soupie-62/SWR_Meter/Notes/circuit-03-KiCad.png

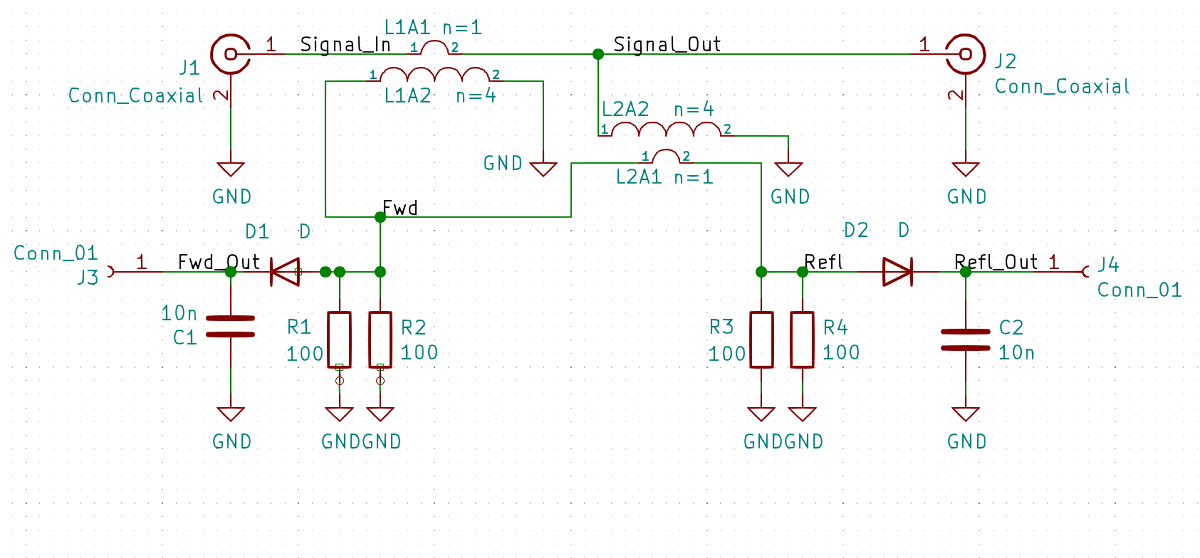
Notes/circuit-03-KiCad.png
