soupie-62/SWR_Meter/Notes/IMG_20211_1_Tin.jpg

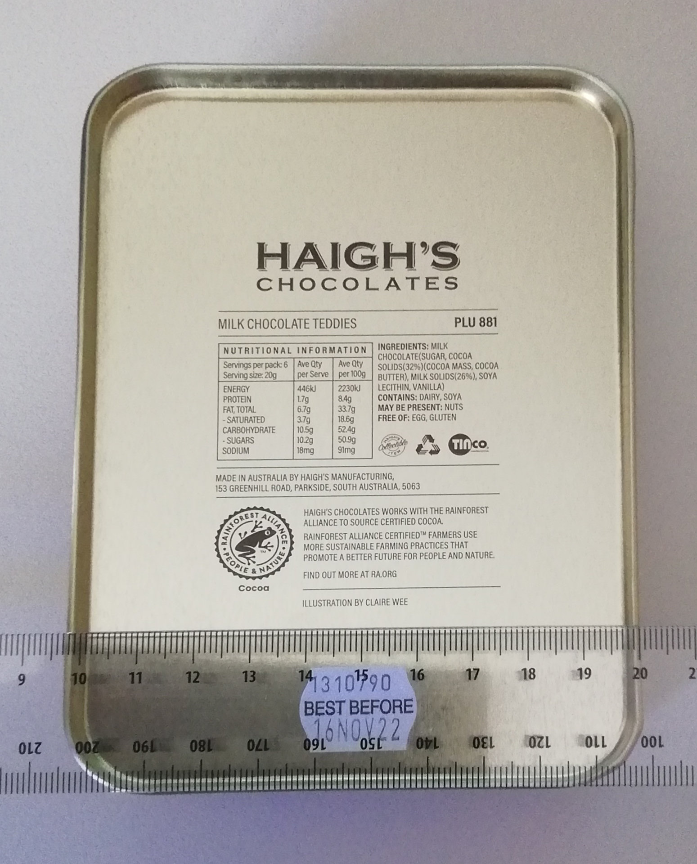
Notes/IMG_20211_1_Tin.jpg
