soupie-62/SWR_Meter/Notes/PCB_Spiral_20GHz_1.png

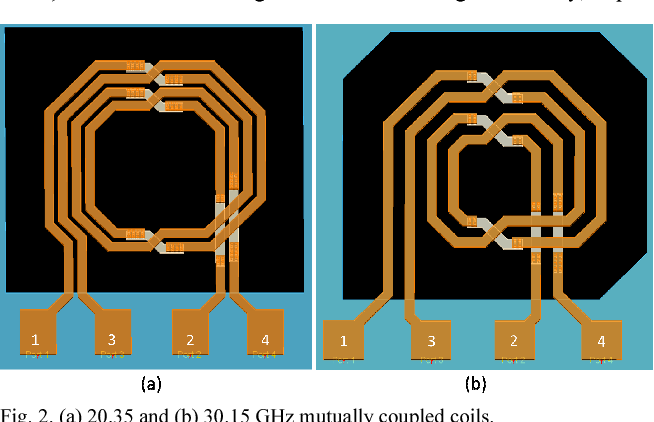
Notes/PCB_Spiral_20GHz_1.png
