soupie-62/SWR_Meter/Notes/S-Parameters - Enrico Lia 1.jpg

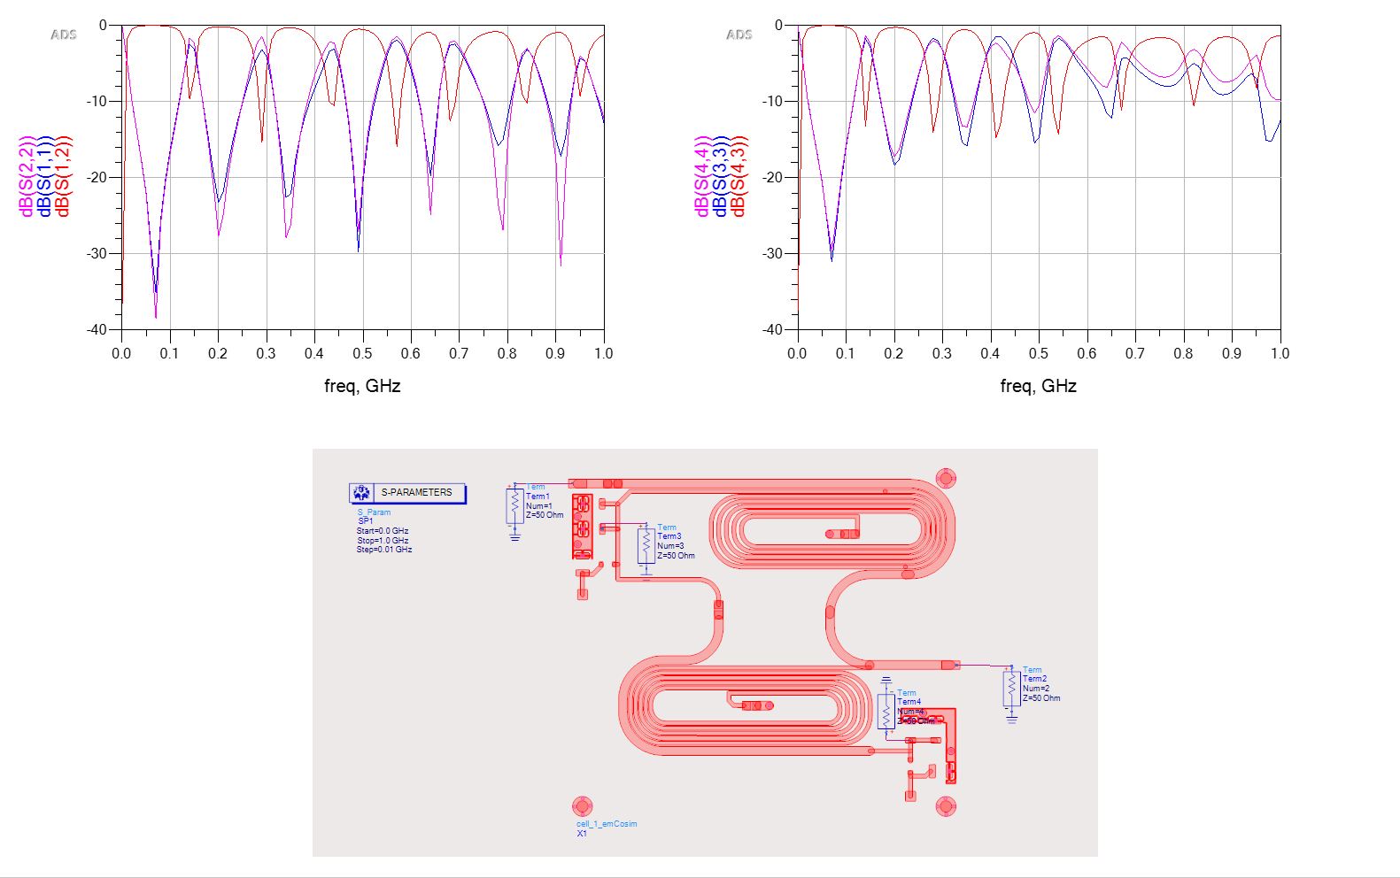
Notes/S-Parameters - Enrico Lia 1.jpg
