soupie-62/SWR_Meter/Notes/S-Parameters - Enrico Lia 2 [CST Studio].jpg

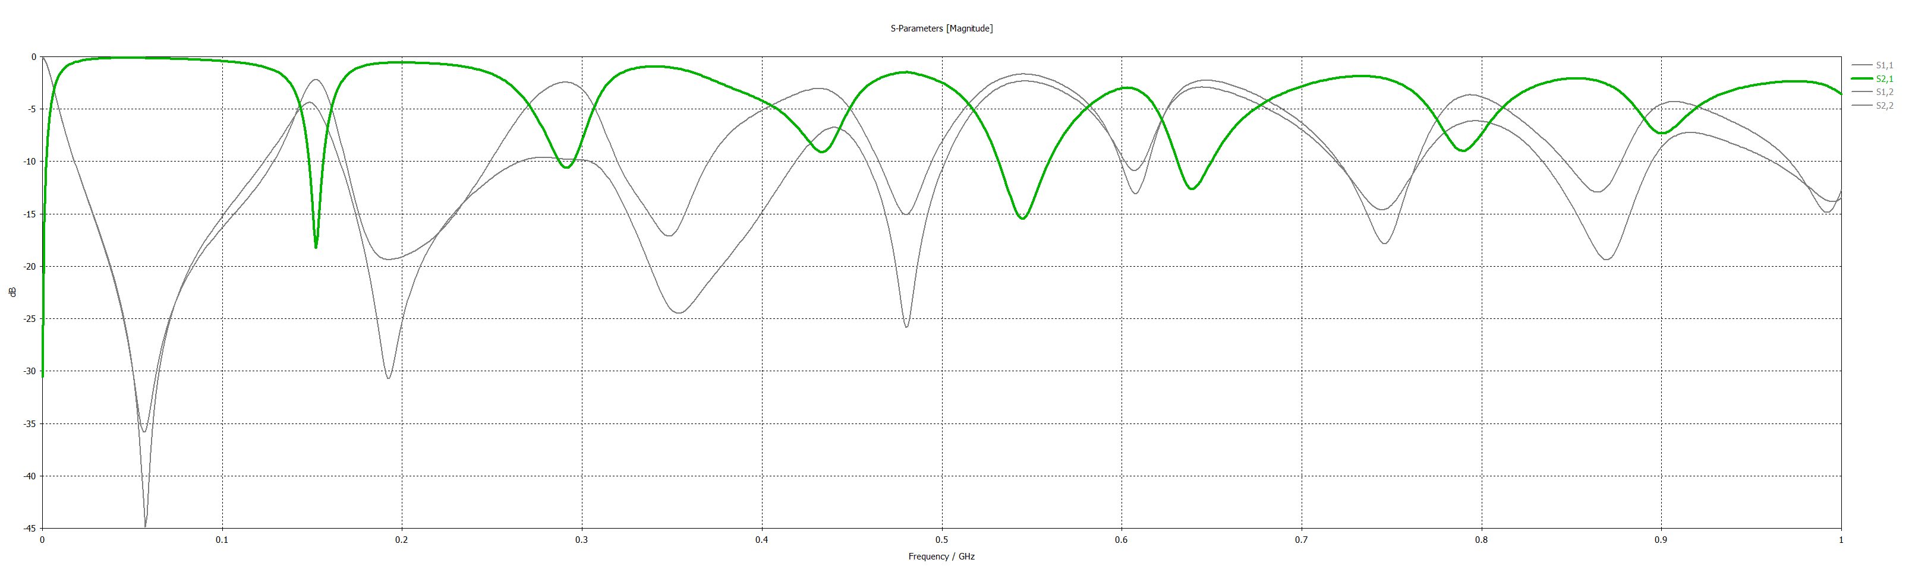
Notes/S-Parameters - Enrico Lia 2 [CST Studio].jpg
