soupie-62/SWR_Meter/Notes/SWR_pcb_V1.png

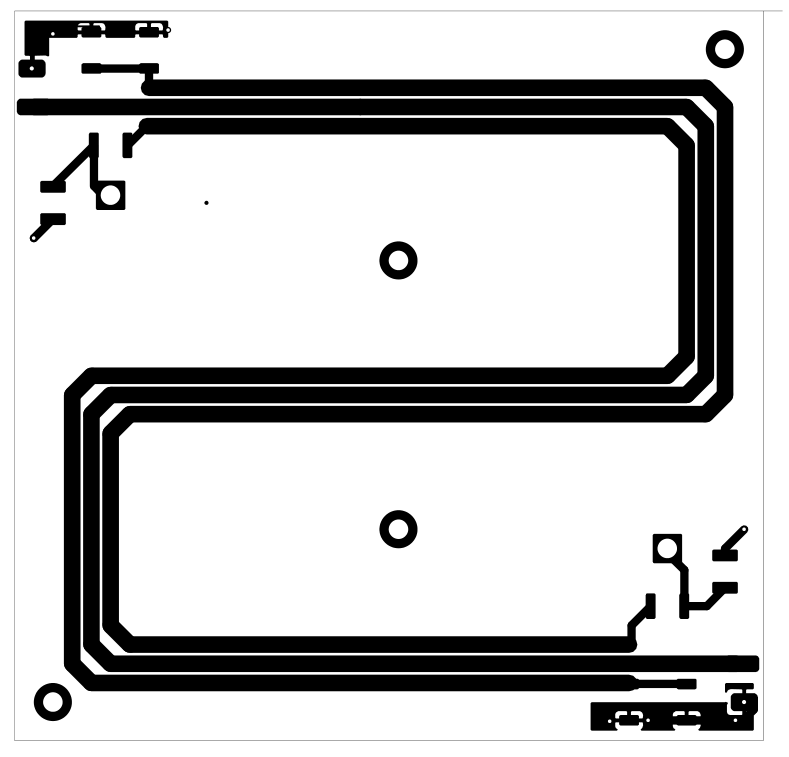
Notes/SWR_pcb_V1.png
