soupie-62/SWR_Meter/Notes/SWR_pcb_V2-3.png

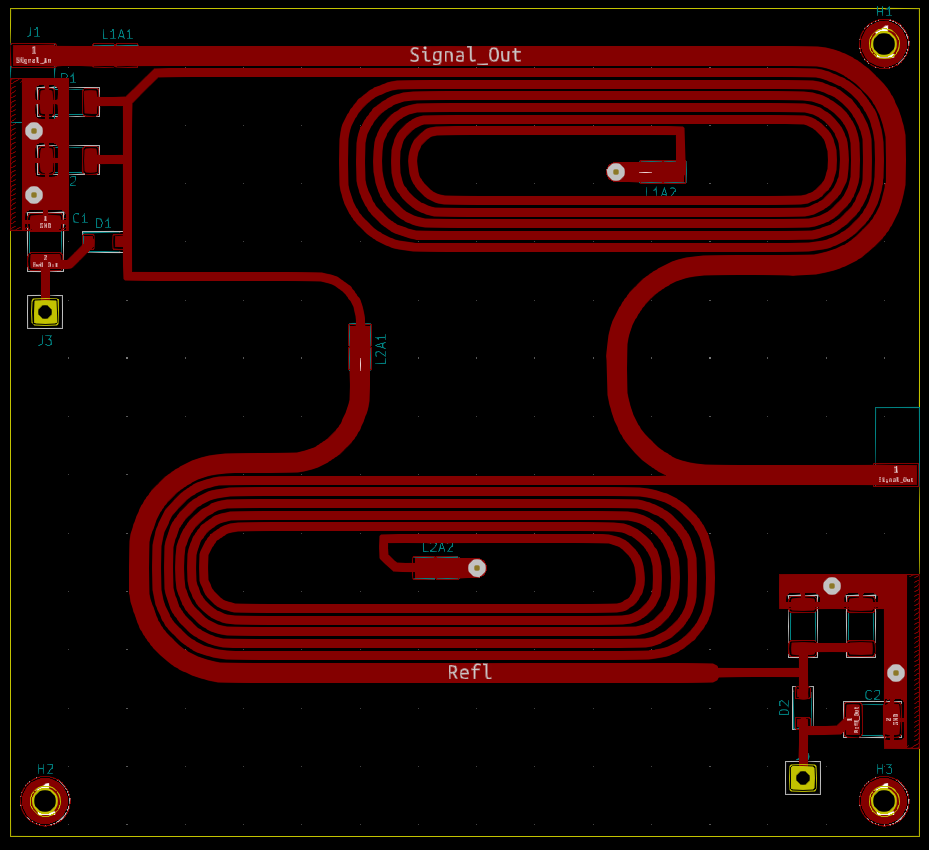
Notes/SWR_pcb_V2-3.png
